asallaup/kegsense/hardware/kegdisplay/case_bar_base_preview.png

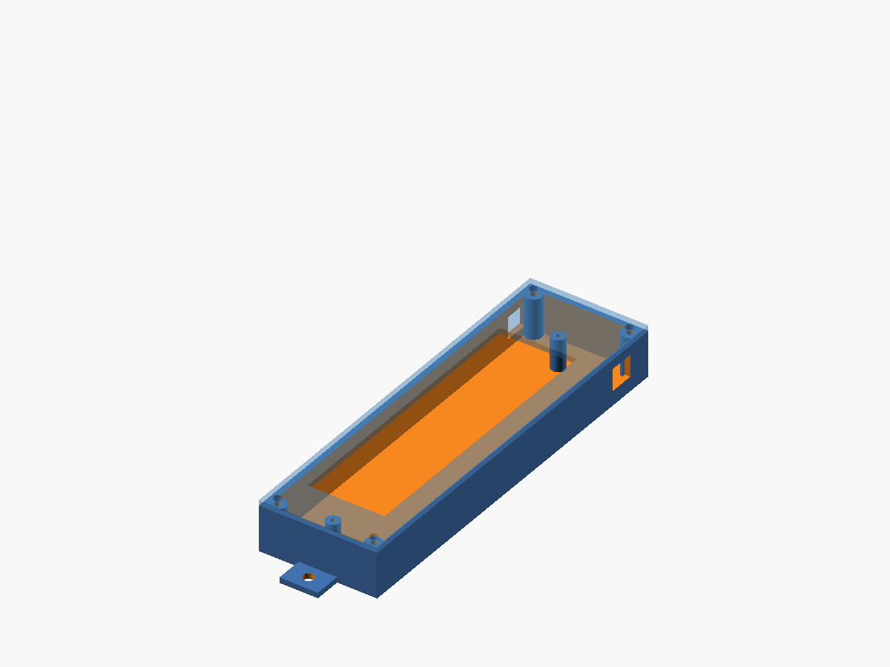
hardware/kegdisplay/case_bar_base_preview.png
