asallaup/kegsense/hardware/kegdisplay/case_bar_lid_preview.png

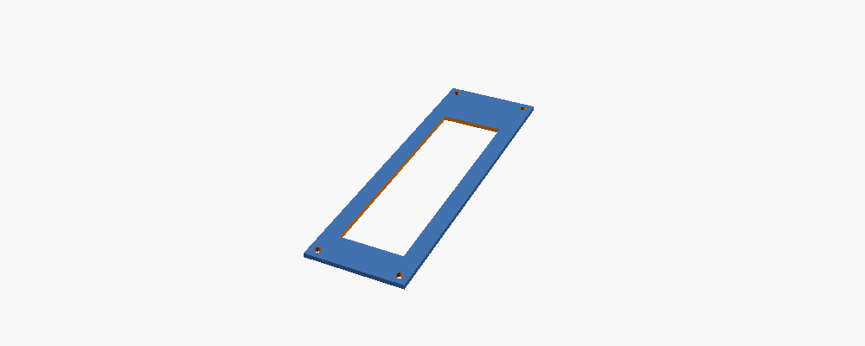
hardware/kegdisplay/case_bar_lid_preview.png
