asallaup/kegsense/hardware/kegdisplay/case_full_back_preview.png

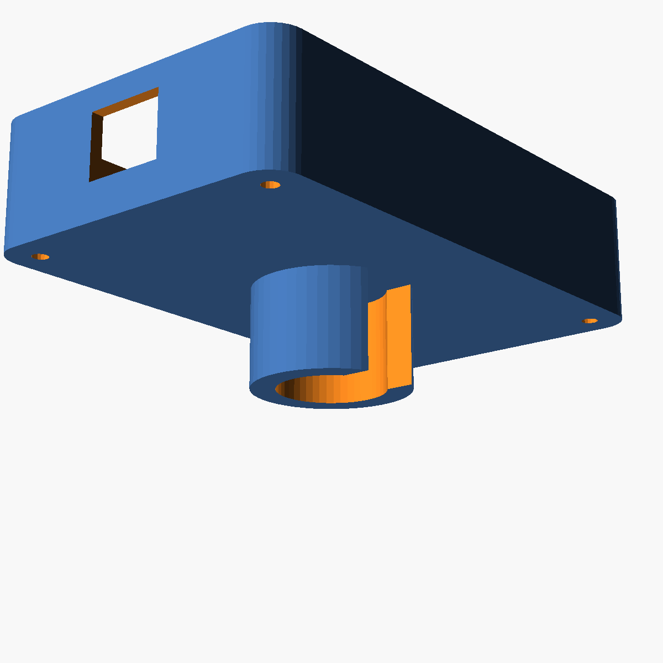
hardware/kegdisplay/case_full_back_preview.png
