asallaup/kegsense/hardware/kegdisplay/keg_display_bar_module_3d.png

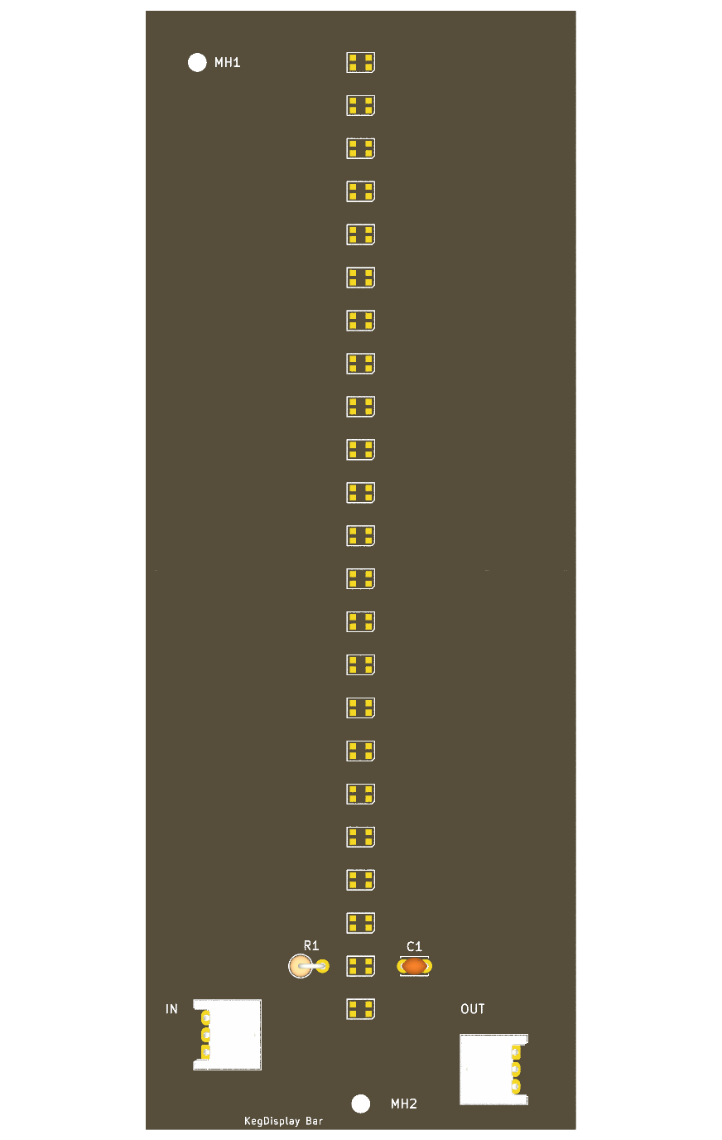
hardware/kegdisplay/keg_display_bar_module_3d.png
