asallaup/kegsense/hardware/kegdisplay/keg_display_module_3d.png

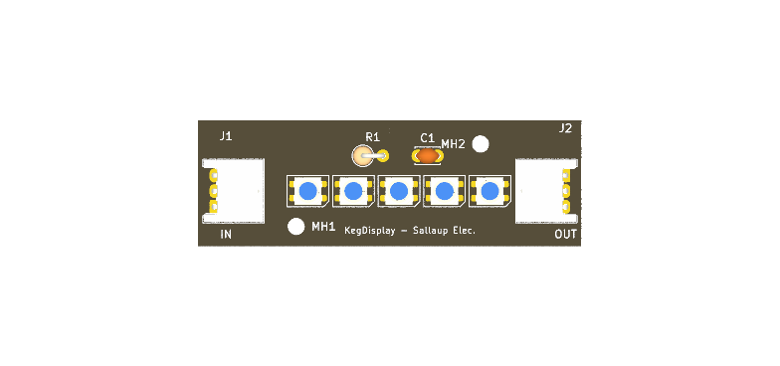
hardware/kegdisplay/keg_display_module_3d.png
