asallaup/kegsense/hardware/kegdisplay/power_protection.png

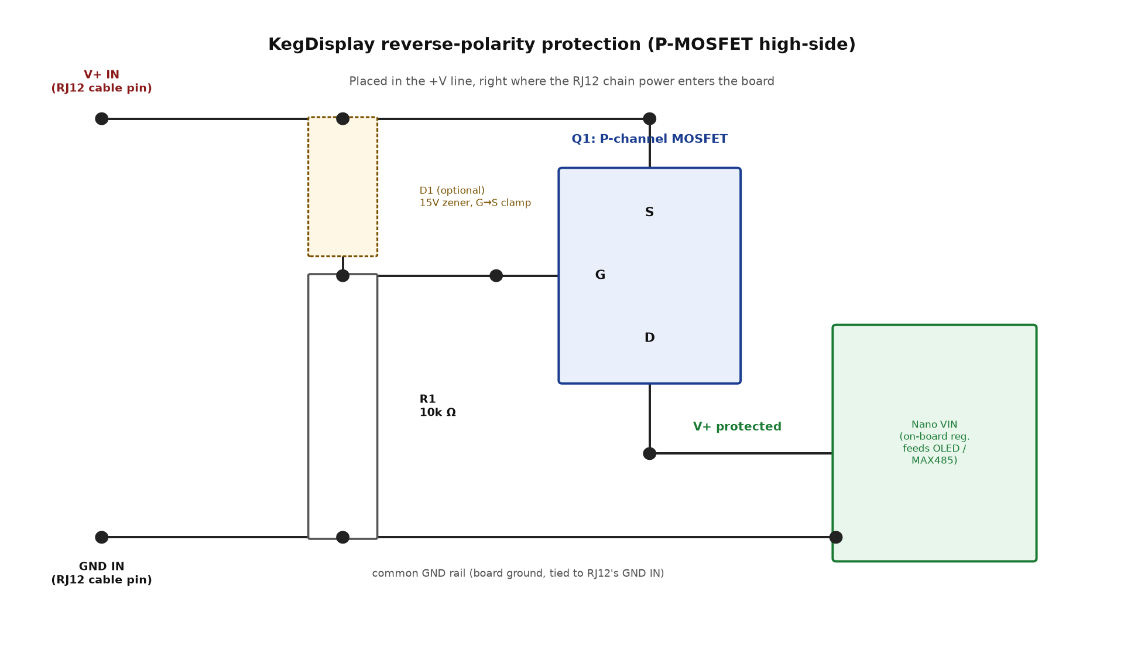
hardware/kegdisplay/power_protection.png
