asallaup/kegsense/hardware/kegsensor/case_base_preview.png

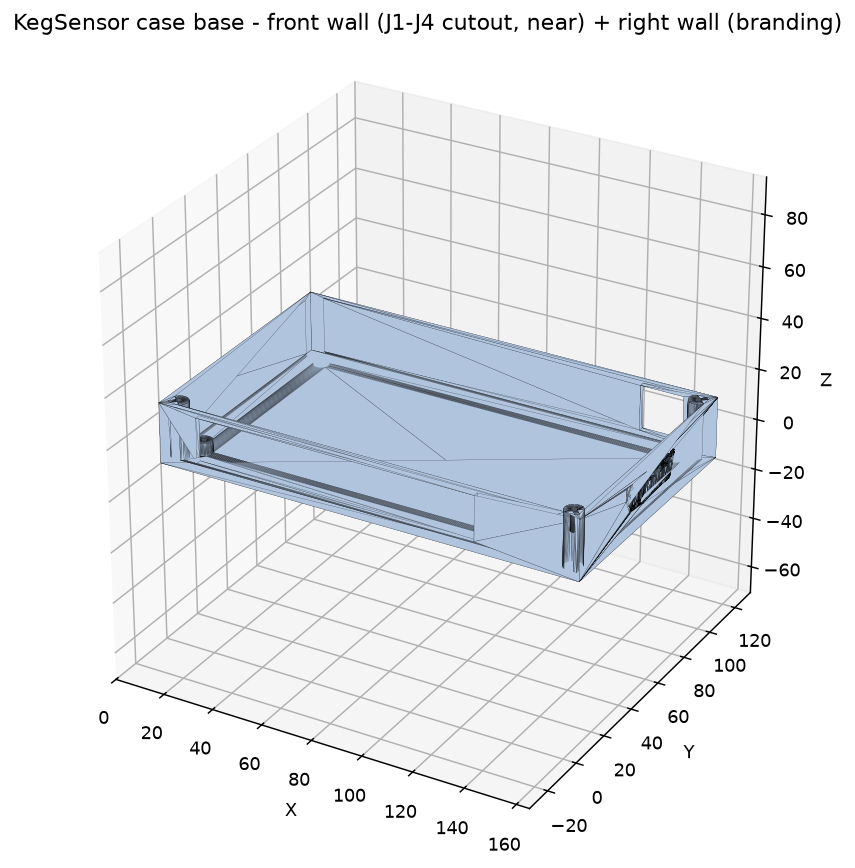
hardware/kegsensor/case_base_preview.png
