asallaup/kegsense/hardware/kegsensor/case_base_preview_2.png

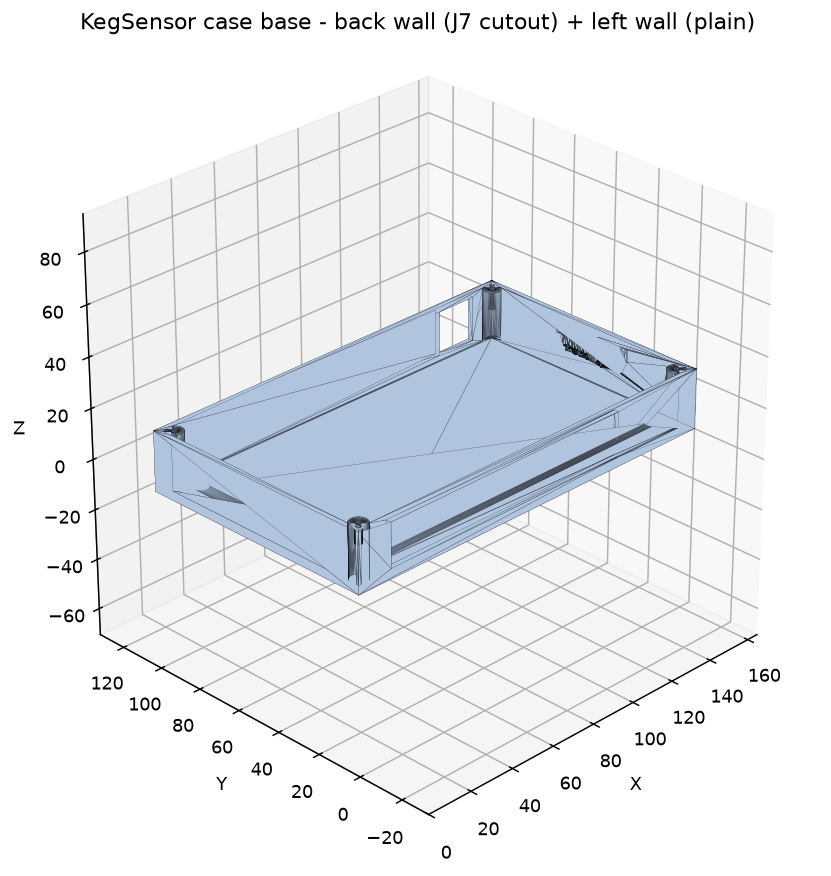
hardware/kegsensor/case_base_preview_2.png
