asallaup/kegsense/hardware/kegsensor/case_engrave_right_preview.png

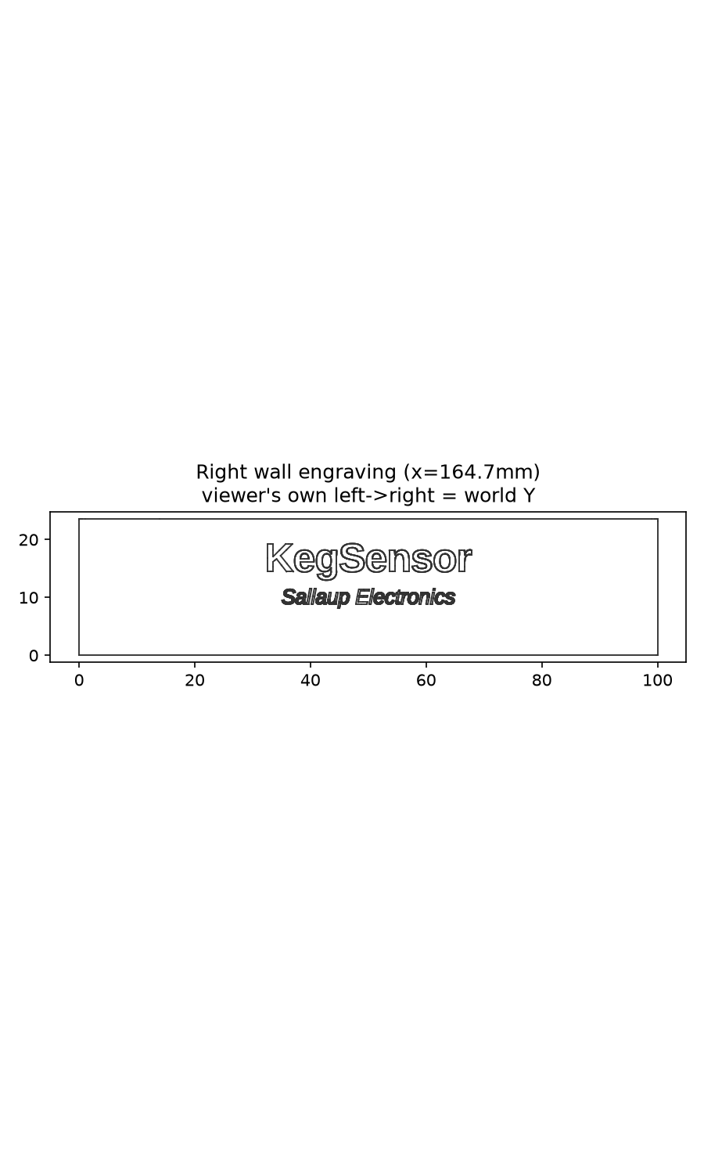
hardware/kegsensor/case_engrave_right_preview.png
