asallaup/kegsense/hardware/kegsensor/load-cell-platform/load_cell_holder_notch_sideview.png

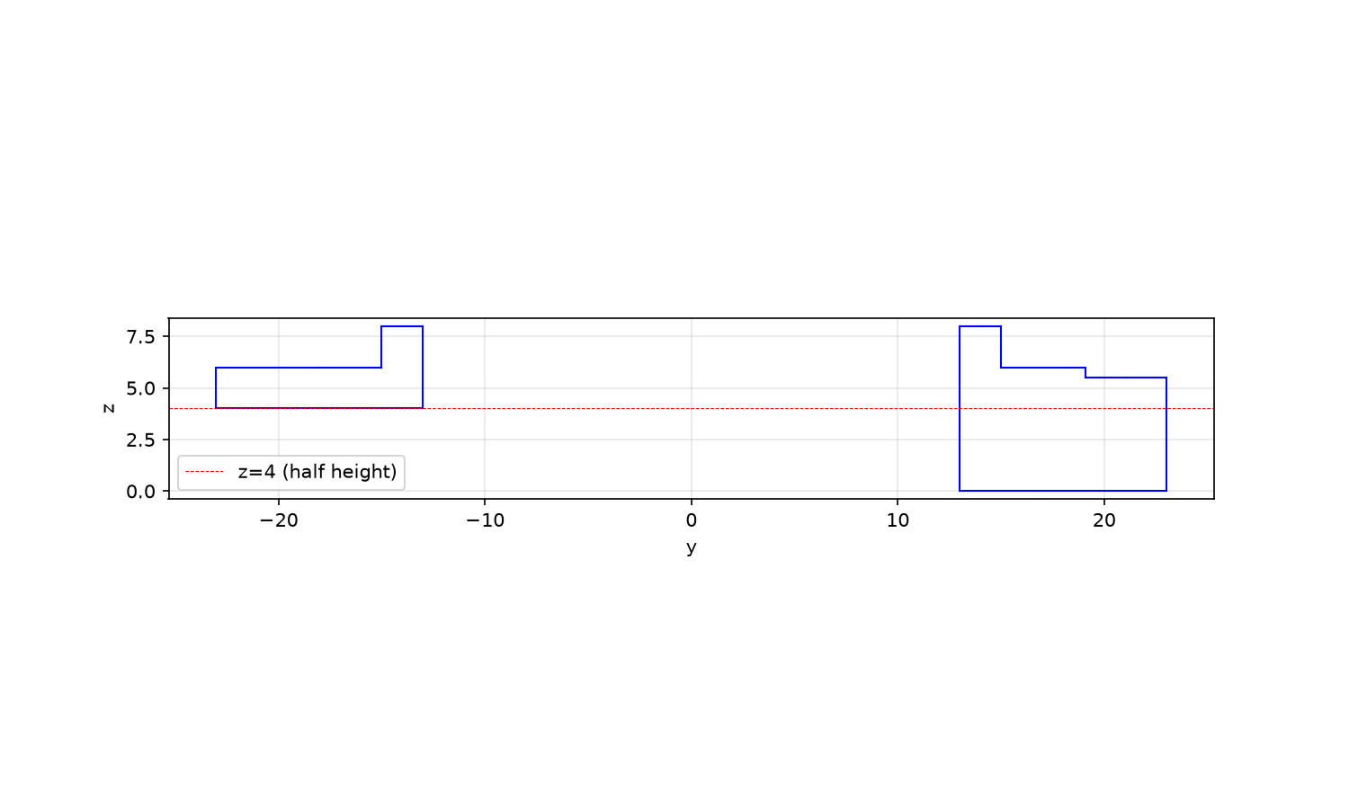
hardware/kegsensor/load-cell-platform/load_cell_holder_notch_sideview.png
