asallaup/kegsense/software/kegstation/assets/sallauprampen.jpg

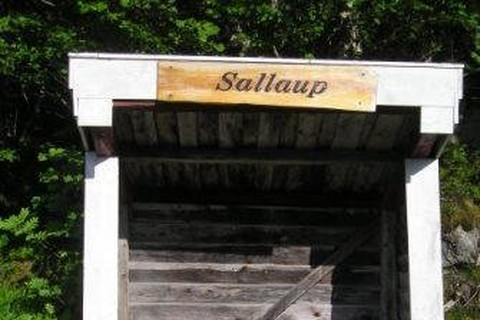
software/kegstation/assets/sallauprampen.jpg
