asallaup/kegsense/software/kegstation/assets/WEB_Image_Corneliusfat_19_liter_100273-cornelius19-20190124-olbryggning-800917965_plid_1440.jpeg

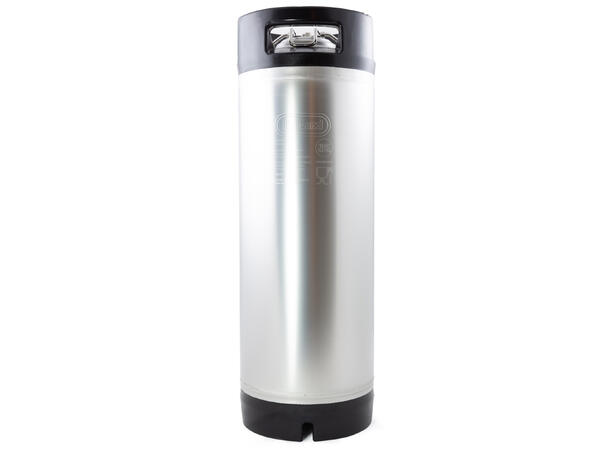
software/kegstation/assets/WEB_Image_Corneliusfat_19_liter_100273-cornelius19-20190124-olbryggning-800917965_plid_1440.jpeg
