asallaup/kegsense/hardware/kegdisplay/case_assembled_preview.png

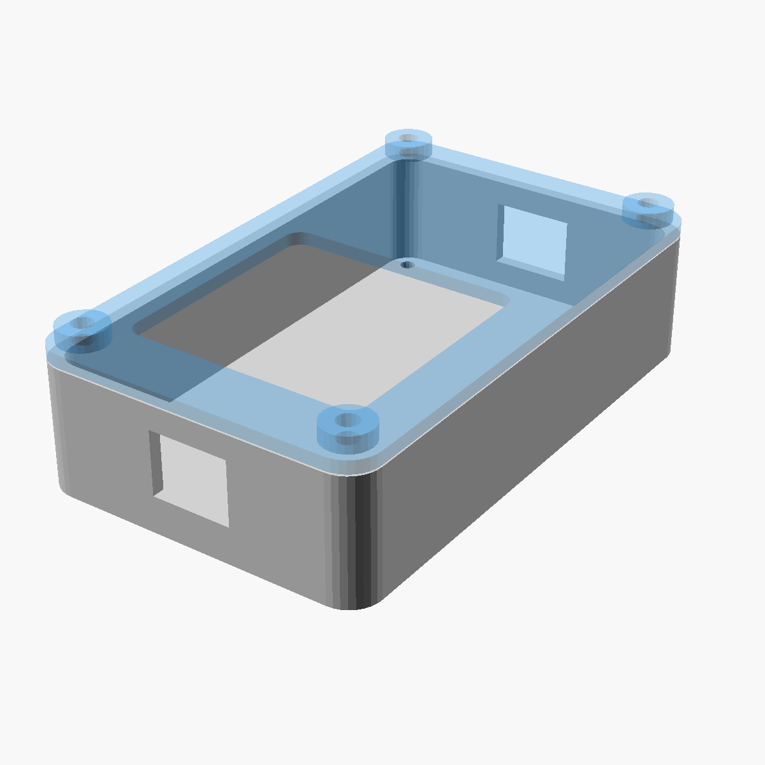
hardware/kegdisplay/case_assembled_preview.png
