asallaup/kegsense/hardware/kegdisplay/enable_wiring_options.png

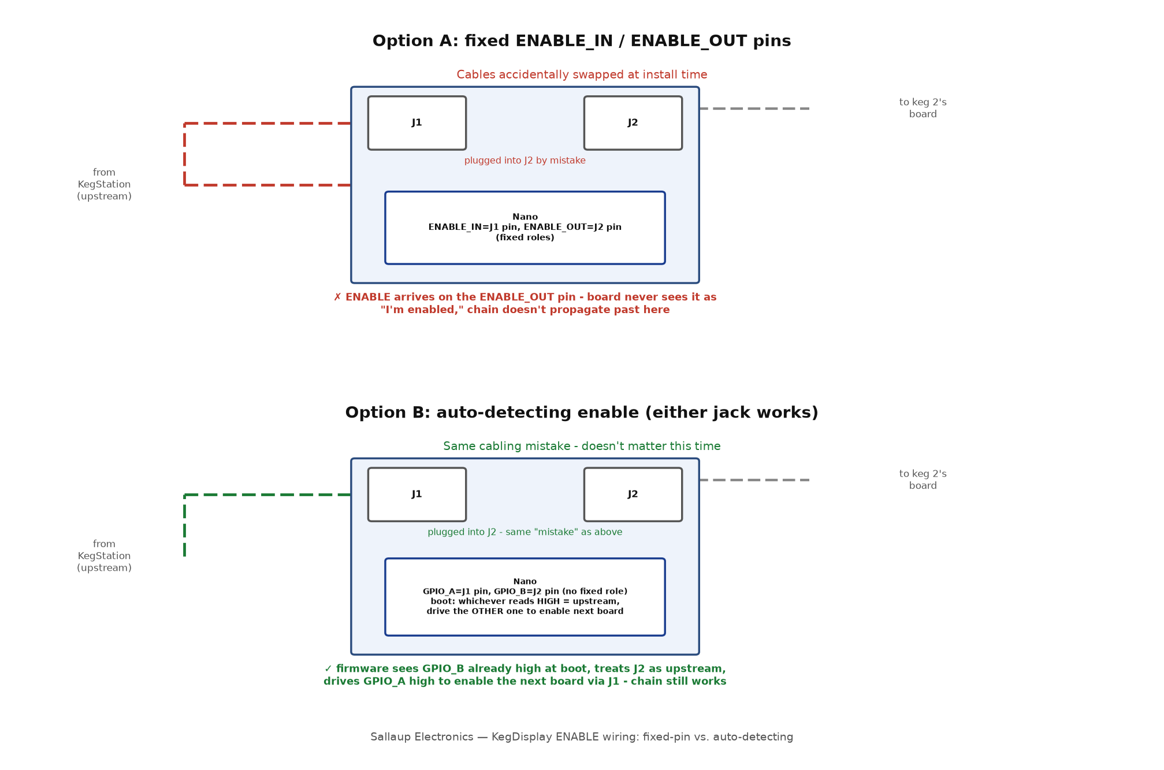
hardware/kegdisplay/enable_wiring_options.png
