asallaup/kegsense/hardware/kegstation/power_wiring_diagram.png

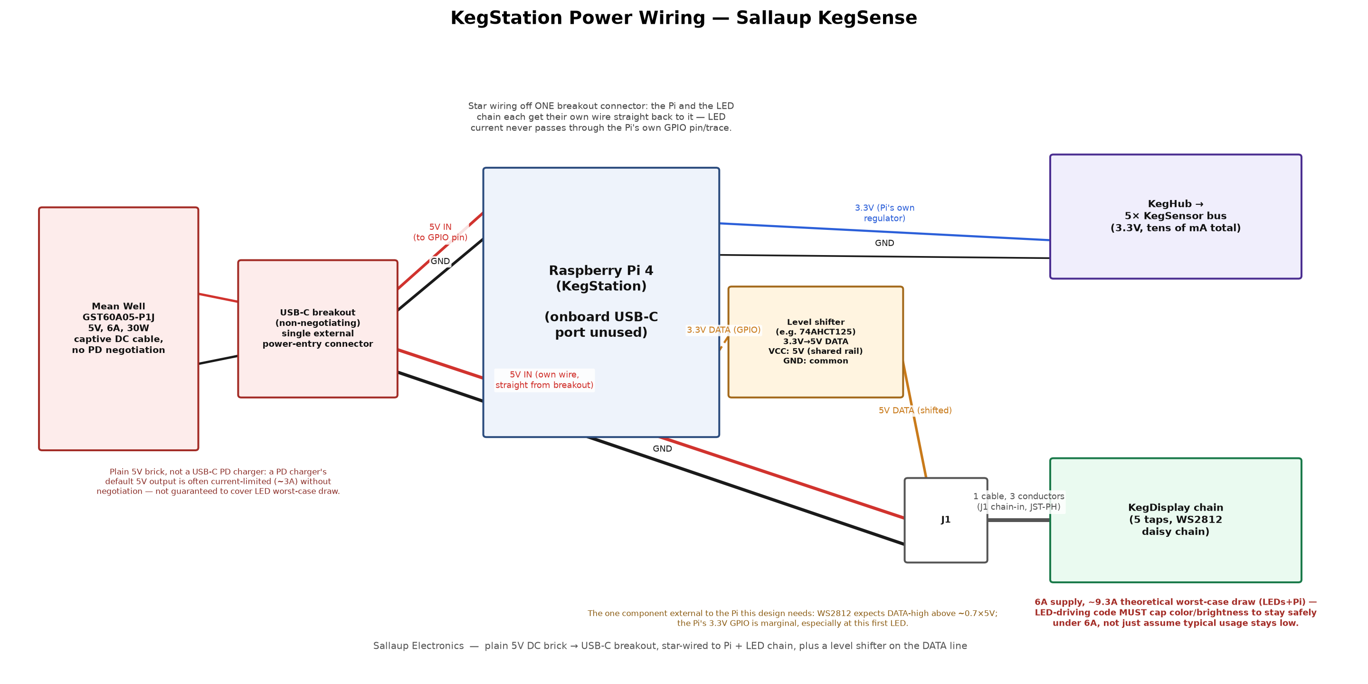
hardware/kegstation/power_wiring_diagram.png
