asallaup/kegsense/hardware/kegsensor/load-cell-platform/load_cell_holder_validation.png

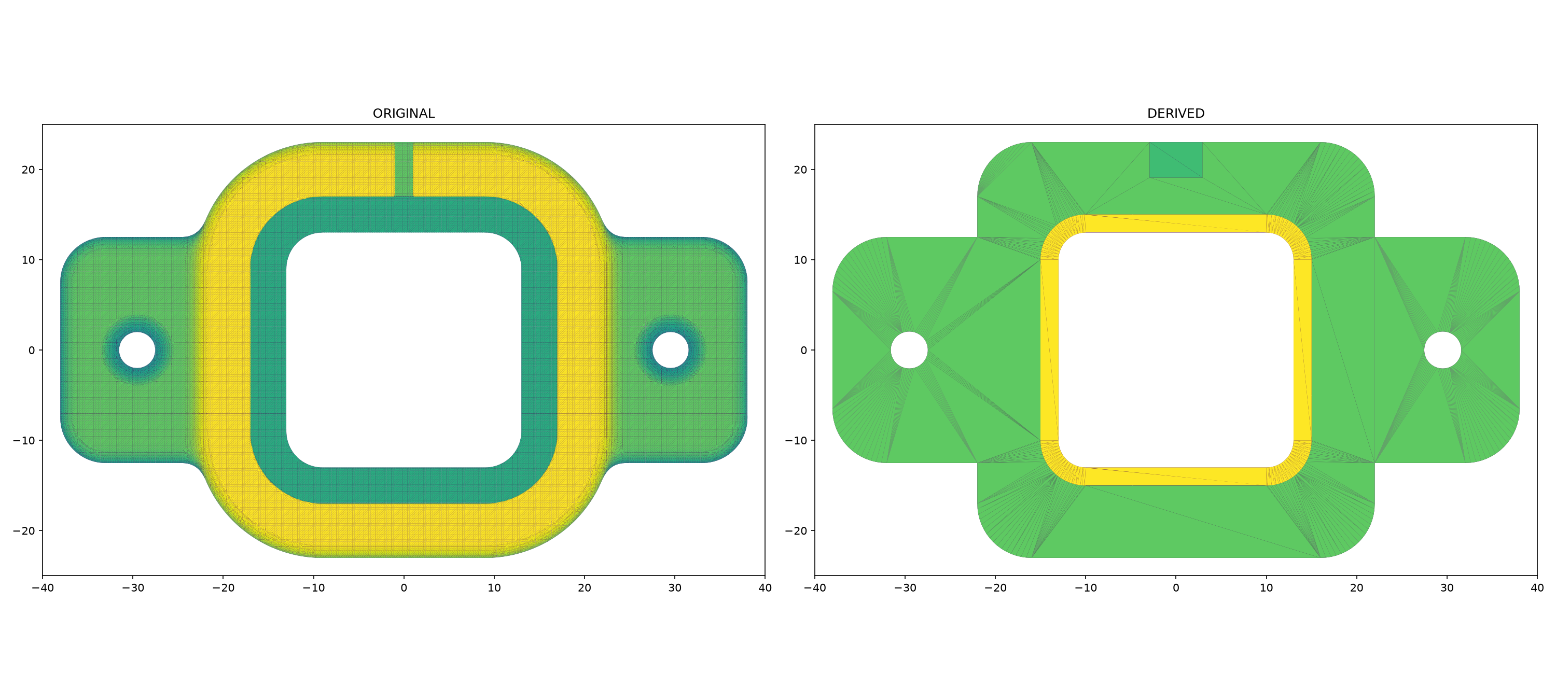
hardware/kegsensor/load-cell-platform/load_cell_holder_validation.png
